Folainer/4-layer-pcb-spi-training-board/src/step3_1.cir

[Main]
FileType=CIR
Version=12.00
Program=Micro-Cap
Component Version=10.00
Shape Version=11.00
Screen=1536,864
MCAPVersion=12.2.0.5
Key ID=Demo
NLCnt=161
TXCnt=15

[shapedef]
Name=92
Block=0,8,56,72,0,8
BlockLine="Line",-16,16
BlockLine="Line",-16,32
BlockLine="InvClock",-16,48
BlockLine="InvClock",-16,64
BlockLine="Line",72,16
BlockLine="Line",72,32
BlockLine="Line",72,48
BlockLine="Line",72,64
FColor=None

[shapedef]
Name=139
Block=0,8,56,72,0,8
BlockLine="Line",-16,16
BlockLine="Line",-16,32
BlockLine="None",-16,48
BlockLine="Inv",-16,64
BlockLine="Inv",72,16
BlockLine="Inv",72,32
BlockLine="Inv",72,48
BlockLine="Inv",72,64
FColor=None

[shapedef]
Name=151
Block=11,16,67,208,0,24
BlockLine="Line",0,24
BlockLine="Line",0,40
BlockLine="Line",0,56
BlockLine="Line",0,72
BlockLine="Line",0,88
BlockLine="Line",0,104
BlockLine="Line",0,120
BlockLine="Line",0,136
BlockLine="Line",0,152
BlockLine="Line",0,168
BlockLine="Line",0,184
BlockLine="Inv",0,200
BlockLine="None",80,24
BlockLine="None",80,40
BlockLine="None",80,56
BlockLine="None",80,72
BlockLine="Inv",80,88
BlockLine="None",80,104
BlockLine="None",80,120
BlockLine="Line",80,136
BlockLine="None",80,152
BlockLine="None",80,168
BlockLine="None",80,184
BlockLine="None",80,200
FColor=None

[shapedef]
Name=165
Block=-8,-8,56,200,0,26
BlockLine="Inv",-24,0
BlockLine="Line",-24,16
BlockLine="Clock",-24,32
BlockLine="None",-24,48
BlockLine="Line",-24,64
BlockLine="Line",-24,80
BlockLine="Line",-24,96
BlockLine="Line",-24,112
BlockLine="Line",-24,128
BlockLine="Line",-24,144
BlockLine="Line",-24,160
BlockLine="Line",-24,176
BlockLine="Line",-24,192
BlockLine="None",72,0
BlockLine="None",72,16
BlockLine="None",72,32
BlockLine="None",72,48
BlockLine="None",72,64
BlockLine="None",72,80
BlockLine="None",72,96
BlockLine="Line",72,112
BlockLine="None",72,128
BlockLine="Inv",72,144
BlockLine="None",72,160
BlockLine="None",72,176
BlockLine="None",72,192
FColor=None

[shapedef]
Name=Animated SPST Switch
Animated SPST Switch=0,-8,48,8
Current=16,8,32,8

[shapedef]
Name=Battery
Line=0,0,22,0
Line=22,-3,22,3
Line=26,-7,26,7
Line=26,0,48,0
Current=32,8,16,8

[shapedef]
Name=Diode
Root="Diode.root",0,0,0

[shapedef]
Name=Diode.root
Line=0,0,20,0
Line=28,0,48,0
Rectangle=18,-8,20,8
PolyClosed=3
PolyLine=20,0
PolyLine=28,-8
PolyLine=28,8
Current=32,16,16,16

[shapedef]
Name=Fixed
Line=8,0,32,0
Line=8,0,0,-8
Line=8,0,0,8

[shapedef]
Name=Ground
Line=0,0,12,0
Line=12,-8,12,8
Line=18,-4,18,4
Line=24,0,24,0

[shapedef]
Name=Nand2
Root="Nand.root",0,0,0

[shapedef]
Name=Nand.root
Line=0,0,8,0
Line=8,20,8,-4
Line=0,16,8,16
Line=25,20,8,20
Line=8,-4,25,-4
Ellipse=40,6,44,10
FColor=None
Line=44,8,48,8
Arc=11,-4,40,20 , 25,24,24,-6

[shapedef]
Name=Resistor
PolyOpen=12
PolyLine=0,0
PolyLine=0,0
PolyLine=12,0
PolyLine=14,-4
PolyLine=18,4
PolyLine=22,-4
PolyLine=26,4
PolyLine=30,-4
PolyLine=34,4
PolyLine=36,0
PolyLine=48,0
PolyLine=48,0
Current=32,8,16,8

[shapedef]
Name=STIM1
Arc=50,-8,62,8 , 56,8,62,0
Arc=50,-8,62,8 , 62,0,56,-8
Line=13,8,57,8
Arc=8,-8,18,8 , 13,-8,8,0
Ellipse=53,-3,59,3
Line=64,0,72,0
Arc=8,-8,18,8 , 8,0,13,8
Line=13,-8,57,-8
Line=56,0,64,0
Line=17,4,22,4
Line=22,4,22,-5
Line=22,-5,29,-5
Line=29,-5,29,4
Line=29,4,33,4
Line=33,4,33,-5
Line=33,-5,36,-5
Line=36,-5,36,4
Line=36,4,41,4
Line=41,4,41,-5
Line=41,-5,43,-5

[shapedef]
Name=StimClock
Arc=50,-8,62,8 , 56,8,62,0
Arc=50,-8,62,8 , 62,0,56,-8
Line=13,8,57,8
Arc=8,-8,18,8 , 13,-8,8,0
Ellipse=53,-3,59,3
Line=64,0,72,0
Arc=8,-8,18,8 , 8,0,13,8
Line=13,-8,57,-8
Line=56,0,64,0
Line=16,4,20,4
Line=20,4,20,-4
Line=20,-4,24,-4
Line=24,-4,24,4
Line=24,4,28,4
Line=28,4,28,-4
Line=28,-4,32,-4
Line=32,-4,32,4
Line=32,4,36,4
Line=36,4,36,-4
Line=36,-4,40,-4
Line=40,-4,40,4
Line=40,4,44,4
Line=44,4,44,-4
Line=44,-4,48,-4
Line=48,-4,48,4
Line=48,4,52,4

[compdef]
Name=7493A
Definition=Subckt
Shape=92
Mask=20608
Used=1
memo=Binary Counters
Label Offset=18,72,-5,16
PinCnt=8
Pin="R01",d,-2,2,18,7
Pin="R02",d,-2,4,18,7
Pin="CKA",d,-2,6,26,7
Pin="CKB",d,-2,8,26,7
Pin="QA",d,9,2,-32,7
Pin="QB",d,9,4,-32,7
Pin="QC",d,9,6,-32,7
Pin="QD",d,9,8,-32,7

[compdef]
Name=74ALS139
Definition=Subckt
Shape=139
Mask=20608
Used=1
memo=Dual 2-Line To 4-Line Decoder/Demultiplexer
Label Offset=29,72,-4,22
PinCnt=7
Pin="1A",d,-2,2,19,7
Pin="1B",d,-2,4,19,7
Pin="1GB",d,-2,8,19,7
Pin="1Y0",d,9,2,-37,7
Pin="1Y1",d,9,4,-37,7
Pin="1Y2",d,9,6,-37,7
Pin="1Y3",d,9,8,-37,7

[compdef]
Name=74251
Definition=Subckt
Shape=151
Mask=20608
Used=1
memo=Data Selectors/Multiplexers With 3-State Outputs
Label Offset=70,32,-62,67
PinCnt=14
Pin="D0",d,0,3,14,7
Pin="W",d,10,11,-24,7
Pin="D1",d,0,5,14,7
Pin="D2",d,0,7,14,7
Pin="D3",d,0,9,14,7
Pin="D4",d,0,11,14,7
Pin="D5",d,0,13,14,7
Pin="D6",d,0,15,14,7
Pin="D7",d,0,17,14,7
Pin="A",d,0,19,14,7
Pin="B",d,0,21,14,7
Pin="C",d,0,23,14,7
Pin="GBAR",d,0,25,14,7
Pin="Y",d,10,17,-22,7

[compdef]
Name=DClock
Definition=Macro
Shape=StimClock
Mask=4096
Used=13
memo=Digital Clock Stimulus Macro
Link=http://www.spectrum-soft.com/news/fall2003/dclock.shtm
Label Offset=29,10,12,21
PinCnt=1
Pin="Out",d,9,0

[compdef]
Name=Ground
Definition=Ground
Shape=Ground
Mask=1793
Used=413
memo=Ground
Label Offset=0,0,0,0
PinCnt=1
Pin="PinA",0,0,-3,-7

[compdef]
Name=Battery
Definition=Battery
Shape=Battery
Mask=6913
Used=199
memo=Battery
Label Offset=19,7,10,13
PinCnt=2
Pin="Plus",6,0,-4,-5
Pin="Minus",0,0,-10,-5

[compdef]
Name=74HC165
Definition=Subckt
Shape=165
Mask=20608
Used=7
memo=Parallel-Load 8-Bit Shift Register
Label Offset=59,40,-80,56
PinCnt=14
Pin="SH/LDBAR",d,-3,0,19,7
Pin="QH",d,9,14,-33,7
Pin="QHBAR",d,9,18,-53,7
Pin="CLK_INH",d,-3,2,19,7
Pin="CLK",d,-3,4,26,7
Pin="SER",d,-3,8,19,7
Pin="A",d,-3,10,19,7
Pin="B",d,-3,12,19,7
Pin="C",d,-3,14,19,7
Pin="D",d,-3,16,19,7
Pin="E",d,-3,18,19,7
Pin="F",d,-3,20,19,7
Pin="G",d,-3,22,19,7
Pin="H",d,-3,24,19,7

[compdef]
Name=Fixed Digital
Definition=DIGITAL STATE
Shape=Fixed
Mask=2048
Used=13
memo=Provides a fixed digital state
Label Offset=-14,-7,-6,-27
PinCnt=1
Pin="Out",4,0,-8,-3

[compdef]
Name=Stim1
Definition=STIM
Shape=STIM1
Mask=4099
Used=14
Data2=1
memo=1-Bit Digital Stimulus
Label Offset=-10,-6,13,20
PinCnt=1
Pin="Out0",9,0,-5,-3

[compdef]
Name=74H00
Definition=Subckt
Shape=Nand2
Mask=4224
Used=1
memo=Quad 2-Input Nand Gates
Label Offset=13,20,8,8
PinCnt=3
Pin="1A",d,0,0,-5,-2
Pin="1Y",d,6,1,-7,-3
Pin="1B",d,0,2,-5,-1

[compdef]
Name=Resistor
Definition=Resistor
Shape=Resistor
Mask=7169
Used=692
memo=Resistor
Label Offset=18,6,8,11
PinCnt=2
Pin="Plus",6,0,-10,-4
Pin="Minus",0,0,-14,-4

[compdef]
Name=Animated SPST Switch
Definition=ANIMATED SPST SWITCH
Shape=Animated SPST Switch
Mask=4352
Used=82
memo=Animated Single Pole, Single Throw Switch
Label Offset=2,5,11,11
PinCnt=2
Pin="A",0,0,5,0
Pin="B",6,0,-10,1

[compdef]
Name=Diode
Definition=Diode
Shape=Diode
Mask=5377
Used=83
memo=Diode
Label Offset=17,10,12,12
PinCnt=2
Pin="Anode",6,0,-9,-8
Pin="Cathode",0,0,-20,-8

[Circuit]
Window Placement=2,3, -1,-1, -8,-31, 41,213,1008,567
Default Object=Color=#000080
Default Object Font=Height=-15,FStyle=0,Color=#000080,Name=Arial
Default Object Apply Border To Text=No
Default Object Apply Fill To Text=No
Default Object GridSnap=No
NodeVoltageFormat=3
CurrentFormat=3
PowerFormat=3
PathDelayFormat=3
WarningFormat=3
GridTextFormulaFormat=3
Window Placement in Transient Analysis=0,1, -1,-1, -8,-31, 0,0,761,629
SpiceType=AMBIGUOUS
Title_Block_Border=None
Title_Block=True
Show Nodes=True
Show Voltages=False
Show Current=False
Show Power=False
Show Condition=False
Show Pin Connections=False
Show Connection Warnings=False
Show Cross=False
Show Attribute Text=False
Show Grid Text=True

[Comp]
Name=7493A
Style=ShowPinText
Px=672,432

[Attr]
ON=18,72,PART
V=X1
Style=8192

[Attr]
ON=18,86,NAME
V=7493A
Style=12288

[Attr]
ON=18,114,PACKAGE
V=DIP14

[Comp]
Name=74ALS139
Style=ShowPinText
Px=848,464

[Attr]
ON=29,72,PART
V=X2
Style=8192

[Attr]
ON=29,86,NAME
V=74ALS139

[Attr]
ON=29,114,PACKAGE
V=DIP16

[Attr]
ON=29,128,GATE
V=A

[Attr]
ON=29,142,COMPNAME
V=UX2

[Comp]
Name=74251
Style=ShowPinText
Px=1080,584
Rot=1

[Attr]
ON=-35,40,PART
V=X3
Style=8192

[Attr]
ON=70,46,NAME
V=74251
Style=4096

[Attr]
ON=70,74,PACKAGE
V=DIP16

[Comp]
Name=DClock
Px=560,480

[Attr]
ON=-9,-9,PART
V=X4
Style=8192

[Attr]
ON=29,24,FILE
V=DClock

[Attr]
ON=29,52,Param:ZEROWIDTH
V=10u

[Attr]
ON=29,66,Param:ONEWIDTH
V=10u

[Attr]
ON=0,0,PACKAGE
V

[Comp]
Name=Ground
Px=944,224
Rot=1

[Comp]
Name=Battery
Px=944,224

[Attr]
ON=18,-23,PART
V=V1
Style=8192

[Attr]
ON=19,8,VALUE
V=5
Style=8192

[Attr]
ON=0,0,PACKAGE
V

[Wire]
Pxs=920,496,928,496

[Wire]
Pxs=920,528,928,528

[Wire]
Pxs=920,480,928,480

[Wire]
Pxs=632,480,656,480

[Wire]
Pxs=744,448,816,448

[Wire]
Pxs=816,552,928,552

[Wire]
Pxs=928,552,928,584

[Wire]
Pxs=744,464,800,464

[Wire]
Pxs=800,568,912,568

[Wire]
Pxs=912,568,912,584

[Wire]
Pxs=744,480,784,480

[Wire]
Pxs=744,496,768,496

[Wire]
Pxs=816,448,816,520

[Wire]
Pxs=800,464,800,568

[Wire]
Pxs=656,520,816,520

[Wire]
Pxs=792,584,832,584

[Wire]
Pxs=832,528,832,584

[Wire]
Pxs=976,400,976,496

[Wire]
Pxs=920,512,928,512

[Wire]
Pxs=960,336,960,480

[Wire]
Pxs=960,336,1096,336

[Wire]
Pxs=1024,552,1024,584

[Wire]
Pxs=1040,560,1192,560

[Wire]
Pxs=1040,560,1040,584

[Wire]
Pxs=1056,576,1264,576

[Wire]
Pxs=832,584,880,584

[Wire]
Pxs=1056,576,1056,584

[Wire]
Pxs=928,528,1096,528

[Wire]
Pxs=928,512,992,512

[Wire]
Pxs=928,496,976,496

[Wire]
Pxs=928,480,960,480

[Wire]
Pxs=816,520,816,552

[Wire]
Pxs=1008,544,1008,584

[Comp]
Name=74HC165
Style=ShowPinText
Px=856,232

[Attr]
ON=59,40,PART
V=X5
Style=8192

[Attr]
ON=59,54,NAME
V=74HC165

[Attr]
ON=59,82,PACKAGE
V=DIP16

[Wire]
Pxs=816,312,816,448

[Wire]
Pxs=816,312,832,312

[Wire]
Pxs=800,328,800,464

[Wire]
Pxs=800,328,832,328

[Wire]
Pxs=784,344,832,344

[Wire]
Pxs=784,344,784,480

[Wire]
Pxs=784,480,832,480

[Wire]
Pxs=768,360,832,360

[Wire]
Pxs=768,360,768,496

[Wire]
Pxs=768,496,832,496

[Comp]
Name=Fixed Digital
Px=760,584

[Attr]
ON=-11,-27,PART
V=U1

[Attr]
ON=-2,-13,VALUE
V=0
Style=12288

[Attr]
ON=-41,1,I/O MODEL
V=IO_STD

[Attr]
ON=-2,15,IO_LEVEL
V=0

[Attr]
ON=-58,29,POWER NODE
V=$G_DPWR

[Attr]
ON=-55,43,GROUND NODE
V=$G_DGND

[Attr]
ON=0,0,PACKAGE
V

[Comp]
Name=Fixed Digital
Px=800,296

[Attr]
ON=-11,-27,PART
V=U2

[Attr]
ON=-7,-6,VALUE
V=0
Style=8192
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
CBorder=None

[Grid Text]
Text="QA"
Px=744,448
GridSnap=True
JustifyH=Left
JustifyV=Bottom
CBorder=None

[Grid Text]
Text="QC"
Px=744,480
GridSnap=True
JustifyH=Left
JustifyV=Bottom
CBorder=None

[Grid Text]
Text="QD"
Px=744,496
GridSnap=True
JustifyH=Left
JustifyV=Bottom
CBorder=None

[Grid Text]
Text="QB"
Px=744,464
GridSnap=True
JustifyH=Left
JustifyV=Bottom
CBorder=None

[Grid Text]
Text="0"
Px=784,304
GridSnap=True
JustifyH=Left
JustifyV=Bottom
CBorder=None

[Grid Text]
Text="0"
Px=584,440
GridSnap=True
JustifyH=Left
JustifyV=Bottom
CBorder=None

[Schematic]
CurrentSection 0=0
CurrentSection 1=0
CurrentSection 2=0
CurrentSection 3=0
Splitter.xs=0
Splitter.ys=0
TextQuad=4099
Scale=1
GridUser=10
ShapeGroups="Main","Euro","Polarity","Main1","Main11","Electrolytic","GroundArrow","DeMorgan"
CalcRMS=False
CalcAVG=False
CalcPeak=False
CalcVoltage=True
DisplayMeasure=Last
ShareScales=True

[Tools]
Pos=Top
FILESAVEASOLD=No
BOM=No
FILEPCB=No
PROBE=Yes
SELECT=Yes
PAN=Yes
COMP=Yes
TEXT=Yes
WIRE=Yes
WIRED=Yes
BUS=Yes
GRAPHIC=Yes
FLOWCHART=Yes
LINE=No
ELLIPSE=No
RECT=No
DIAM=No
ARC=No
PIE=No
TRIANGLE=No
STAR=No
LEFTBRK=No
RIGHTBRK=No
BOTHBRK=No
META=No
PARALLELOGRAM=No
FC_PROCESS=No
FC_ALT_PROCESS=No
FC_DECISION=No
FC_DATA=No
FC_PREDEFPROCESS=No
FC_INTERNALSTORAGE=No
FC_DOCUMENT=No
FC_MULTIDOCUMENT=No
FC_TERMINATOR=No
FC_PREPARATION=No
FC_MANUALINPUT=No
FC_MANUALOPERATION=No
FC_CONNECTOR=No
FC_OFFPAGECONNECTOR=No
FC_PUNCHCARD=No
FC_PUNCHEDTAPE=No
FC_SUMMING_JUNCTION=No
FC_OR=No
FC_COLLATE=No
FC_SORT=No
FC_EXTRACT=No
FC_MERGE=No
FC_STORED_DATA=No
FC_DELAY=No
FC_SAS=No
FC_MAGNETIC_DISK=No
FC_DAS=No
FC_DISPLAY=No
SPREAD_SHEET=Yes
POLYCLOS=No
POLYOPEN=No
FLAG=Yes
INFO=Yes
HELP=Yes
HELP_SPICE=No
LINK=Yes
CHECK=Yes
REGION_ENABLE=Yes
TITLE_BLOCK=Yes
DIGTRC=No
DIGTRC2=No
BUILD_COMMAND=Yes
DIGALL=No
GRIDTEXT=Yes
COMPTEXT=Yes
NODE=Yes
MEASURED=Yes
NODEV=Yes
CURRENT=Yes
POWER=Yes
CONDITIN=Yes
PIN=Yes
CONNWARN=Yes
CROSS=No
GRID=Yes
BORDER=Yes
BORDERONE=Yes
TITLE=Yes
RUBBER=Yes
PROPERTY=Yes
STEP=Yes
MIRROR=Yes
ROTATE=Yes
FLIPY=Yes
FLIPX=Yes
CIR_MAKEMACRO=No
CLEARCUTWIRE=No
CLIPBOARDCIRPAGE2BMM=No
FINDCOMP=Yes
FIND=Yes
REPEAT=No
REPLACE=No
MODEL=Yes
CIR2CKT=No
ATTDISP=No
ENABLE=Yes
DISABLE=Yes
ENABLE_WITH=Yes
TOFRONT=Yes
TOBACK=Yes
SELNEXT=No
PAGEADD=No
PAGEADDTEXT=No
ADDSECTION=No
PAGEDEL=No
ZOOMIN=Yes
ZOOMOUT=Yes
AUTOSCALECIR=Yes
GOTOFLAG=No
UPLEVEL=Yes
COLOR=Yes
FONT=Yes
STYLE=Yes
DM_LAST=No
DM_RMS=No
DM_AVG=No
DM_PEAK=No
GRID_NONE=No
GRID_NORMAL=No
GRID_BOLD_5=No
GRID_BOLD_6=No
GRID_BOLD_USER=No
GRAPH_PAPER=No
SPLITCIRTEXTH=No
SPLITCIRTEXTV=No
SPACE_SPLITTERS_EVENLY=No
NORMALCIR=No
RENAMEDEFINE=No
RENAMECMP=No
ATTALIGN=No
RESETNODEPOS=No
FIT2STANDARD=No
NODESNAP=No
MOVETEXT=No
TEXTINC=No
TOGGLETEXT=No
TOGGLEMODE=No
TOLERANCE=No
ALIGNAB=No
ALIGNLEFT=No
ALIGNCENTER=No
ALIGNRIGHT=No
ALIGNTOP=No
ALIGNMIDDLES=No
ALIGNBOTTOM=No

[Section]
Index=0
Name="circuit1"
Type=Main
Enable=True
CurrentPage 0=0
CurrentPage 1=0
CurrentPage 2=0
CurrentPage 3=0
TabSize 0=425
TabSize 1=425
TabSize 2=425
TabSize 3=425

[Page]
Index=0
Section=0
Print=True
Enable=True
Name=Main
PrinterScale=1
Scale 0=1
Scale 1=1
Scale 2=1
SB 3=646,205
Scale 3=1
Px=1315,503
WinBackGround Color=#FFFFFF
Select Color=#FF0000
Anchor Color=#000000
Select Box Color=#000080
Grid Text Color=Height=-12,FStyle=0,Color=#0000FF,Name=Verdana
Grid Text RTF=False
Grid Text Angle=0
Grid Text GridSnap=True
Grid Text PinIt=False
Grid Text JustifyH=Left
Grid Text JustifyV=Bottom
Grid GradientColor2=None
Grid OutlineThickness=1
Grid OutlineColor=None
Component Color=#0000FF
Attribute Text=Height=-12,FStyle=0,Color=#008000,Name=Verdana
Wire Color=#008000
Bus Color=#008000
Pin Connection=Height=-10,FStyle=0,Color=#FF0000,Name=Arial
Pin Marker Color=#008000
Node Number=Height=-11,FStyle=0,Color=#FF00FF,Name=Arial
Node Voltage Color=Height=-11,FStyle=0,Color=#000000,Name=Arial
Dynamic AC Voltage Color=#E4E4E4
Text Banner Text=Height=-15,FStyle=0,Color=#800000,Name=Arial
Title Block Background=#C0C0C0
Current=Height=-11,FStyle=0,Color=#0000FF,Name=Arial
Power/Condition=Height=-11,FStyle=0,Color=#FF0000,Name=Arial
Digital Path Color=#FF0000
Title Block Border=#000000
Disabled	Color=#C0C0C0
Search Color=#FFFF00
Grid Color=#000000
Graph Paper=#E4E4E4
Digital 0 Color=#000000
Digital R Color=#FFFF00
Digital F Color=#FFFF00
Digital 1 Color=#FF0000
Digital X Color=#C0C0C0
Digital Z Color=#808080
Block Select Color=#51F998

[Page]
Index=1
Section=0
Type=Text
Print=False
Enable=True
Name=Text
Font=Height=-15,FStyle=0,Color=#000000,Name=Courier New
Comment Color=#008000
WinBackGround Color=#FFFFFF
Disabled	Color=#C0C0C0
KeyWord Color=#0000FF
Error	Color=#FF0000
Search Color=#FFFF00

[Page]
Index=2
Section=0
Type=Text
Print=False
Enable=True
Name=Models
Font=Height=-15,FStyle=0,Color=#000000,Name=Courier New
Comment Color=#008000
WinBackGround Color=#FFFFFF
Disabled	Color=#C0C0C0
KeyWord Color=#0000FF
Error	Color=#FF0000
Search Color=#FFFF00

[Page]
Index=3
Section=0
Type=Info
Print=False
Enable=True
Name=Info
Font=Height=-15,FStyle=0,Color=#000000,Name=Courier New
Comment Color=#008000
WinBackGround Color=#FFFFFF
Disabled	Color=#C0C0C0
KeyWord Color=#0000FF
Error	Color=#FF0000
Search Color=#FFFF00

[Text Area]
Section=0
Page=1
Text=
Text=.DEFINE _WR 0N 1 30N 0
Text=
Text=.DEFINE _R2 0N 0 50N 1
Text=
Text=.DEFINE _JK 0n 1
Text=
Text=.DEFINE _One 0n 1 100n 0
Text=
Text=.define _q 0n 1

[Text Area]
Section=0
Page=2
Text=* Schematic File
Text=*
Text=* Syntax:
Text=* .MODEL <model name> [AKO:<reference model name>] <ModelType>
Text=* +([<parameter name>=<value>][LOT[/#][/GAUSS|/UNIFORM|/WCASE]=[<tol>[%]] |[-<low>%,<high>%]][DEV[/#][/GAUSS|/UNIFORM|/WCASE]=[<tol>[%]]...)
Text=* ModelType must be one of OPA,D,NPN,NMOS,NJF,PUL,SIN,TRN,CORE,GASFET,VSWITCH,ISWITCH,CAP,IND,RES,PNP,PMOS,PJF,DOUTPUT,DINPUT,UADC,UDAC,UGATE,UTGATE,UEFF,UGFF,UDLY,UPLD,UROM,URAM,UBGT,UIO,LPNP,NIGBT,I,V
Text=*
Text=*Examples:
Text=* .MODEL 2N2222A NPN(BF=150 IS=1E-14)
Text=* .model M1 NMOS(KP=2.5E-5 VTO=1.345 CGDO=14.67p CGBO=4.566p)
Text=* .MODEL DK D(IS=1E-18)
Text=* .model 2N2222A AKO:2N2222 NPN (BF=55 ISE=10F)
Text=* .Model BJT1 NPN (RE=12 LOT/1/GAUSS=30% DEV/2/UNIFORM=2%)
Text=*
Text=* A .cir file is typically found in the data directory
Text=*

[InfoPage]
InfoPage=True
Warnings=True
System=True
Defines=True
Array=True
Model=True
Measure=True
MacroSubckt=True
NotUsed=True
ComponentCounts=True
VariablizePaths=False
DontShowPaths=False
SimulationLog=True

[Transient]
WinID=1
Window Placement=0,1, -1,-1, -8,-31, 761,0,1522,629
Font=Height=-19,FStyle=0,Color=#0000FF,Name=Arial
WinBackGround Color=#FFFFFF
Select Color=#FF0000
Anchor Color=#000000
Select Box Color=#000080
Title=5_SWITCH.cir
AutoTitle=Yes
Grid Color=#808080
Grid Weight=1
Grid Pattern=Dot6
Tracker Foreground=Height=-15,FStyle=0,Color=#000000,Name=Arial
Tracker Background=#FFFF00
Baseline color=#0000FF
BaseLine Weight=1
CurveFit color=#FF0000
CurveFit Weight=2
CurveFit Pattern=Dash
Static Grids=False
PlusMark=False
MinorLog25=Off
LabelMinor=Off
DataPoints=False
Token=False
Ruler=False
XAxisGrids=True
YAxisGrids=True
MinorLogGrids=True
BaseLine=False
AlignZ=True
Align Cursors=True
TagFormatX=3
TagFormatY=3
FormulaFormat=2
EndMode=SCALE
Graph Background=#FFFFFF
Tracker Intercept=False
Tracker Mouse=True
Tracker Cursor=True
Tracker Cursor BranchInfo=False
Horizontal Cursor=False
Same Y Scales=Yes
Enable X Scaling=True
Enable Y Scaling=True
Keep X Scales The Same=True
Number of Grids X=5
Number of Grids Y=5
Cursor Select Color Primary=#C0C0C0
Cursor Select Color Secondary=#FF0000
Data Point Labels Color Fore=Height=-15,FStyle=0,Color=#000000,Name=Arial
Data Point Labels Color Back=#FFFF00
OperPoint=True
OperPointOnly=False
AutoScaleRanges=True
FixedTimeStep=False
DoPSS=False
PSS_Periods="1"
PSS_Iterations="5"
PSS_Error="1u"
PSS_ShowPlots=True
FFT_NPts="8192"
FFT_IncludeDCHarmonic=False
FFT_AutoScale_Harmonics="10"
PrinterAutoTile=No
PrinterBlackBorder=No
MonMaxShow=6
MonPageWidth=66
MonPlotWidth=21
MonExprXWidth=142
MonExprYWidth=367
MonRangeXWidth=90
MonRangeYWidth=90
AnimateWait=None
AnimateWaitTime=500
AnimatePressAfter=0
Save_For_Future=No
Reduce_Display=1
Reduce_Save=1
Reduce_ThrowDataOut=0
Num Out Header Left
Num Out Header Center="$MC\n$user\n$company\n$Analysis of $name\n$date $time"
Num Out Header Right
Num Out Delimiter=32
Num Out Write=True
Num Out Write Main Header=True
Num Out Write Limits=True
Num Out Write Branch Header=True
Num Out Write Models=False
Num Out Write Zero Models=True
Num Out Write Undefined Models=True
Num Out Write Operating Point=True
Num Out Write Measurement Values=True
Num Out Write Tolerance Detail=True
Num Out Write Values=True
Num Out Write Waveform Header=True
Num Out Allow Dup Y Expr=False
Num Out Low="TSTART"
Num Out High="TMAX"
Num Out Font=Height=-15,FStyle=0,Color=#000000,Name=Courier New
Num Out Format=3
Num Out HideNonSelected=False
Num Out UseActualDataPoints=False
AutoSaveWave=False
Wave Format=16E
State Variables Format=5E
Print Individual Pages=False
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
